lilnetty43/esp32-s3-rf-devboard_akel/docs/images/pcb_routing/In1.Cu.png

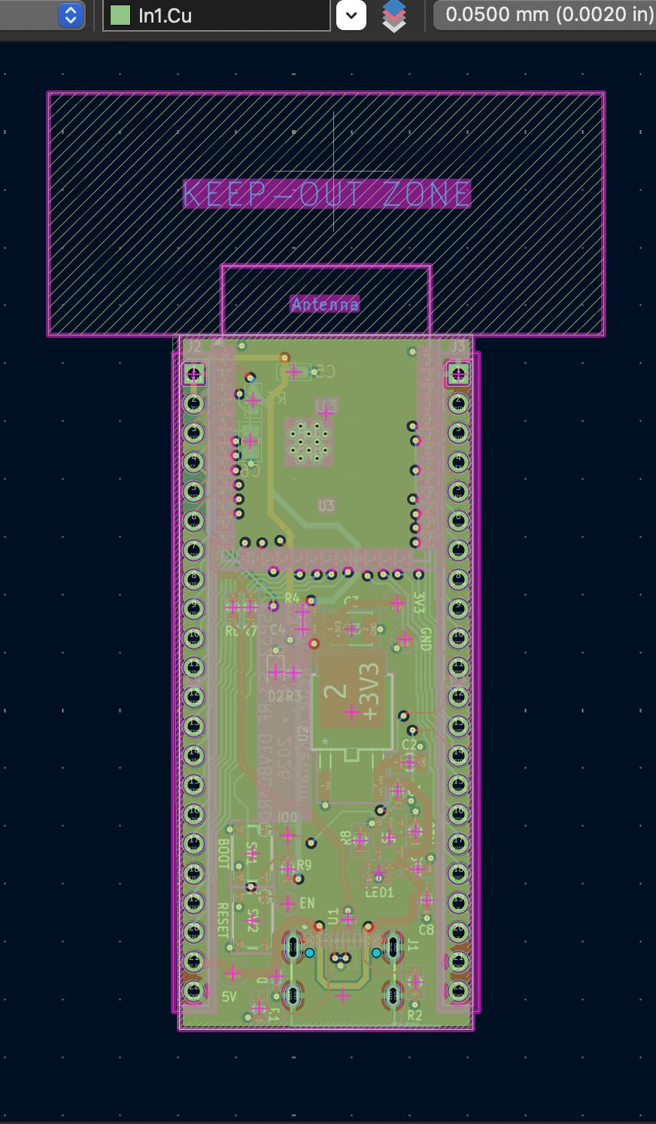
docs/images/pcb_routing/In1.Cu.png
